GhanGhan/Variable_Voltage_Controller/Spice_Designs/Power_Selector/PMUX_Final_Design.asc

B: voltage; 3.3
C1: cap; 0.1µ
C2: cap; 0.1µ
D1: schottky; BAT54
D2: schottky; BAT54
D3: schottky; BAT54
M1: pmos; AO6407
M2: pmos; AO6407
M3: nmos; AO6408
M4: nmos; AO6408
M5: pmos; AO6407
M6: pmos; AO6407
M7: nmos; AO6408
R1: res; 50k
R2: res; 50k
R3: res; 50k
R5: res; 330
R6: res; 50k
R7: res; 100k
R8: res; 100k
R9: res; 100k
R10: res; 100k
S: voltage; 3.3
U1: LTC6702
Named nets: 0, C, S, B, O, SD, BT, ST, CB, CS
.tran 1 startup
