GhanGhan/Variable_Voltage_Controller/Spice_Designs/Reverse_Voltage_ORing/Reverse_V_with_PMOS.asc

D1: diode; 1N914
M1: pmos; AO6407
R1: res; 100k
R2: res; 100
R3: res; 1k
V1: voltage; -6
Named nets: 0, I, O
.tran 1
