GhanGhan/Variable_Voltage_Controller/Program/VVC/Core/Inc/NHD_lcd_config.h

/*
 * NHD_lcd_config.h
 *
 *  Created on: Aug 21, 2025
 *      Author: Ghani
 */

#ifndef INC_NHD_LCD_CONFIG_H_
#define INC_NHD_LCD_CONFIG_H_


#define NUM_CHAR_ROWS 4
#define NUM_COLS 128
#define NUM_BYTES_PER_CHAR 5


#endif /* INC_NHD_LCD_CONFIG_H_ */
