GhanGhan/Variable_Voltage_Controller/Program/VVC/Core/Inc/float2string.h

/*
 * string2float.h
 *
 *  Created on: Aug 22, 2025
 *      Author: Ghani
 */

#ifndef INC_FLOAT2STRING_H_
#define INC_FLOAT2STRING_H_

#include <stdint.h>

// Following functions adapted  from https://www.geeksforgeeks.org/c/gcvt-convert-float-value-string-c/
void ftoa(float n, char * res, uint8_t afterpoint);
int32_t int_to_str(int32_t x, char str[], uint8_t d);
void reverse(char * str, uint8_t len);



#endif /* INC_FLOAT2STRING_H_ */
